likeablob/macmini/openscad/images/macintosh-mini-part-a_s.png

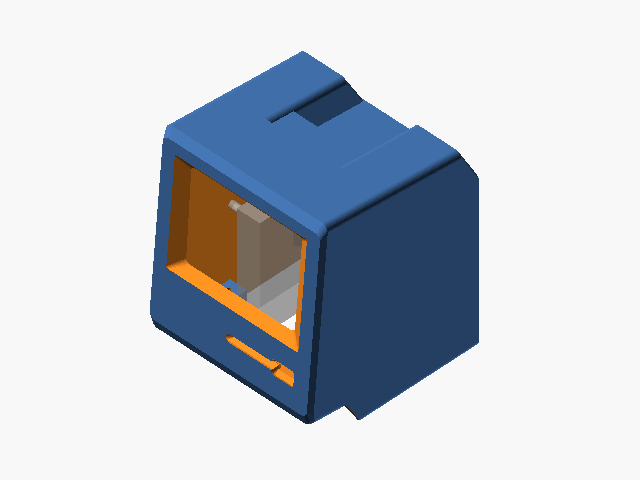
openscad/images/macintosh-mini-part-a_s.png
